PatternAgents/AB_ESP8266/AB_ESP8266/eagleUp/eagleUp_AB_ESP8266_board_bottom.jpg

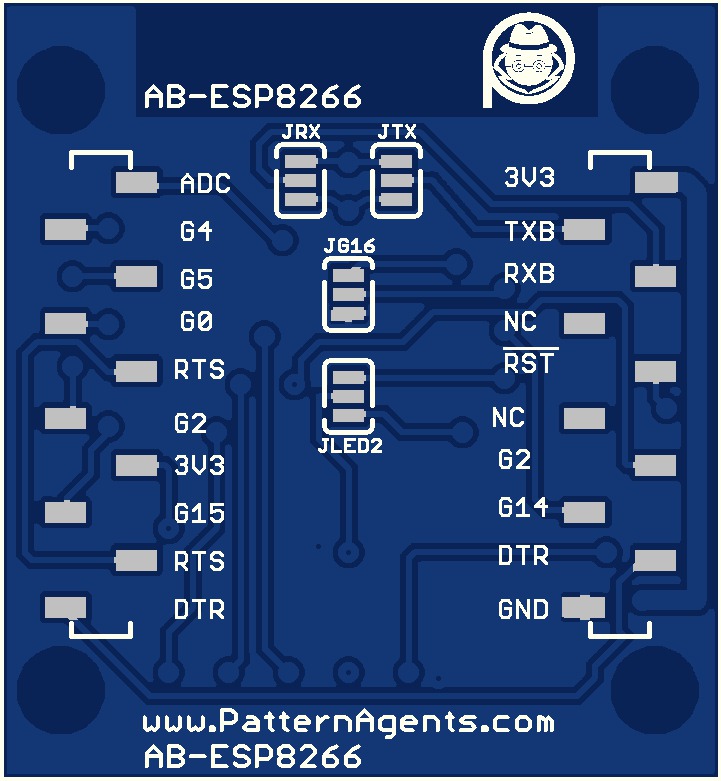
AB_ESP8266/eagleUp/eagleUp_AB_ESP8266_board_bottom.jpg
