PatternAgents/AB_ESP8266/AB_ESP8266/eagleUp/eagleUp_AB_ESP8266_board_top.jpg

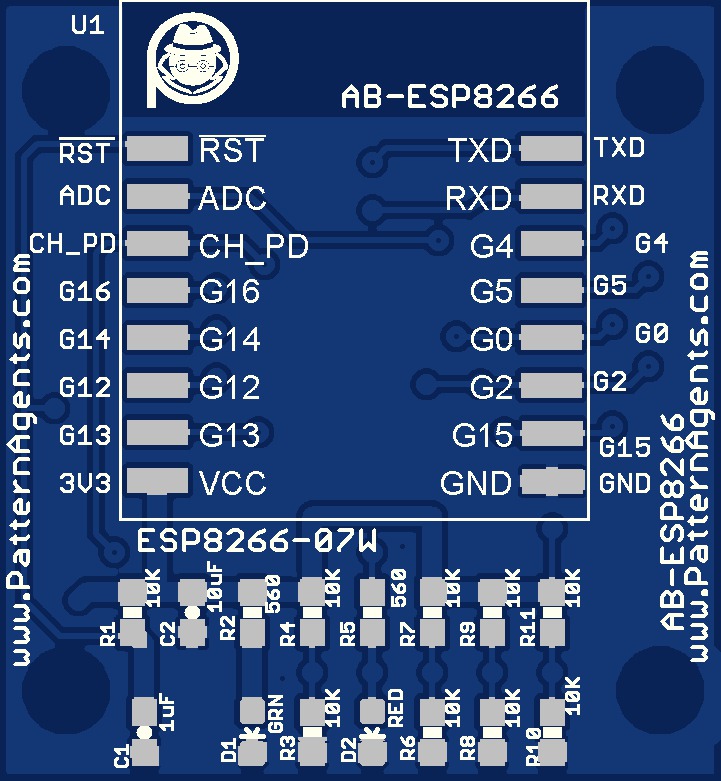
AB_ESP8266/eagleUp/eagleUp_AB_ESP8266_board_top.jpg
